york-fs/precharge/simulation/Discharge.asc

C1: cap; 200µ
R1: res; 188k
R2: res; 1000
R3: res; 8k2
S1: sw; MYSW
S2: sw; MYSW
V1: voltage; 600
V2: voltage; PULSE(0 5 0 0.000001 0.000001 2 4 1)
V3: voltage; PULSE(5 0 0 0.000001 0.000001 2 4 1)
Named nets: 0
.model MYSW SW(Ron=5 Roff=1Meg Vt=2)
.tran 8
