york-fs/precharge/simulation/Draft1.asc

U1: TLV1811
U2: TLV1811
V1: voltage; 5
V2: voltage; 2
V3: voltage; PULSE(0 4 1 0.001 0.001 1 2 4)
V4: voltage; .2
V5: voltage; 5
V6: voltage; 2
V7: voltage; PULSE(0 4 1 0.001 0.001 1 2 4)
V8: voltage; .3
Named nets: 0
.tran 6
