york-fs/precharge/simulation/Precharge complete.asc

C1: cap; 100nF
C2: cap; 1µF
C3: cap; 100nF
C4: cap; 1µF
C5: cap; 100nF
C6: cap; 1µF
C7: cap; 100nF
C8: cap; 1µF
C9: cap; 200µ
D1: diode; 1n4007
D2: diode; 1n4007
D3: diode; 1n4007
M1: nmos; 2n7002
M2: nmos; 2n7002
M3: nmos; 2n7002
M4: nmos; 2n7002
M5: nmos; 2n7002
M6: nmos; 2n7002
M7: nmos; 2n7002
R1: res; 47k
R2: res; 750k
R3: res; 750k
R4: res; 750k
R5: res; 750k
R6: res; 750k
R7: res; 750k
R8: res; 47k
R9: res; 750k
R10: res; 750k
R11: res; 750k
R12: res; 750k
R13: res; 750k
R14: res; 750k
R15: res; 10k
R16: res; 1k
R17: res; 4k
R18: res; 100
R19: res; 1k
R20: res; 4k
R21: res; 10k
R22: res; 100
R23: res; 1k
R24: res; 4k
R25: res; 10k
R26: res; 100
R27: res; 10k
R28: res; 100
R29: res; 188k
R30: res; 1000
Rcoil1: res; 1k
Rcoil2: res; 1k
Rcoil: res; 1k
Shutdown: voltage; 12
U1: AMC1351
U2: AMC1351
V1: voltage; 5
V2: voltage; 12
V3: voltage; 3.3
V4: voltage; 3.3
V5: voltage; 0
V6: voltage; 0
V7: voltage; PULSE(0 480 1 0.000001 0.00001 10)
Named nets: 0, 5V, 12V, 3.3V, TSAL+, TSAL-, TSALp, CAN+, CAN-, Acc+, Acc-, TS+, TS-, Sdwn
*---------- 2N7002 Spice Model ----------
.SUBCKT N7002 10 20 30 
*     TERMINALS:  D  G  S
M1 1 2 3 3 NMOS L = 1E-006 W = 1E-006 
RD 10 1 0.976 
RS 30 3 0.001 
RG 20 2 160.6 
CGS 2 3 2E-011 
EGD 12 0 2 1 1 
VFB 14 0 0 
FFB 2 1 VFB 1 
CGD 13 14 5.9E-011 
R1 13 0 1 
D1 12 13 DLIM 
DDG 15 14 DCGD 
R2 12 15 1 
D2 15 0 DLIM 
DSD 3 10 DSUB 
.MODEL NMOS NMOS LEVEL = 3 VMAX = 1E+006 ETA = 0 VTO = 2.154 
+ TOX = 6E-008 NSUB = 1E+016 KP = 0.4654 KAPPA = 1E-015 U0 = 400 
.MODEL DCGD D CJO = 1.2E-011 VJ = 0.6 M = 0.6 
.MODEL DSUB D IS = 6.808E-010 N = 1.576 RS = 0.1408 BV = 72 CJO = 8E-012 VJ = 0.8 M = 0.6474 
.MODEL DLIM D IS = 0.0001 
.ENDS
*Diodes N7002 Spice Model v0 Last Revised 2017/2/9
STM32
.tran 4
.MODEL 1N4007 D  ( IS=76.9p RS=42.0m BV=1.00k IBV=5.00u
+ CJO=26.5p  M=0.333 N=1.45 TT=4.32u )
