york-fs/precharge/simulation/Precharge sim.asc

C1: cap; 200µ
C2: cap; 200µ
C3: cap; 200µ
C4: cap; 200µ
R1: res; 1000
R2: res; 188k
R3: res; 188k
R4: res; 188k
R5: res; 1000
R6: res; 8k2
R7: res; 188k
R8: res; 1000
R9: res; 8k2
V1: voltage; PULSE(0 600 0 0.000001 0.00001 10)
V2: voltage; PULSE(0 600 1 0.000001 0.00001 10)
V3: voltage; PULSE(0 600 1 0.000001 0.00001 10)
V4: voltage; PULSE(0 600 1 0.000001 0.00001 10)
Named nets: 0
.tran 1.5
