york-fs/precharge/simulation/Voltage Isolator.asc

C1: cap; 100nF
C2: cap; 1µF
C3: cap; 100nF
C4: cap; 1µF
C5: cap; 100nF
C6: cap; 1µF
C7: cap; 100nF
C8: cap; 1µF
C9: cap; 200µ
R1: res; 47k
R2: res; 750k
R3: res; 750k
R4: res; 750k
R5: res; 750k
R6: res; 750k
R7: res; 750k
R8: res; 47k
R9: res; 750k
R10: res; 750k
R11: res; 750k
R12: res; 750k
R13: res; 750k
R14: res; 750k
R29: res; 188k
R30: res; 1000
U1: AMC1351
U2: AMC1351
V1: voltage; 5V
V2: voltage; 12
V3: voltage; 3.3
V7: voltage; PULSE(0 600 1 0.000001 0.00001 10)
Named nets: 0, 5V, 12V, 3.3V, Acc+, Acc-, TS+, TS-
.tran 4
